PradyumnaGudluru/HealthMonotoringSystem/LPEDT-firmware/Screenshots/advertising_period.png

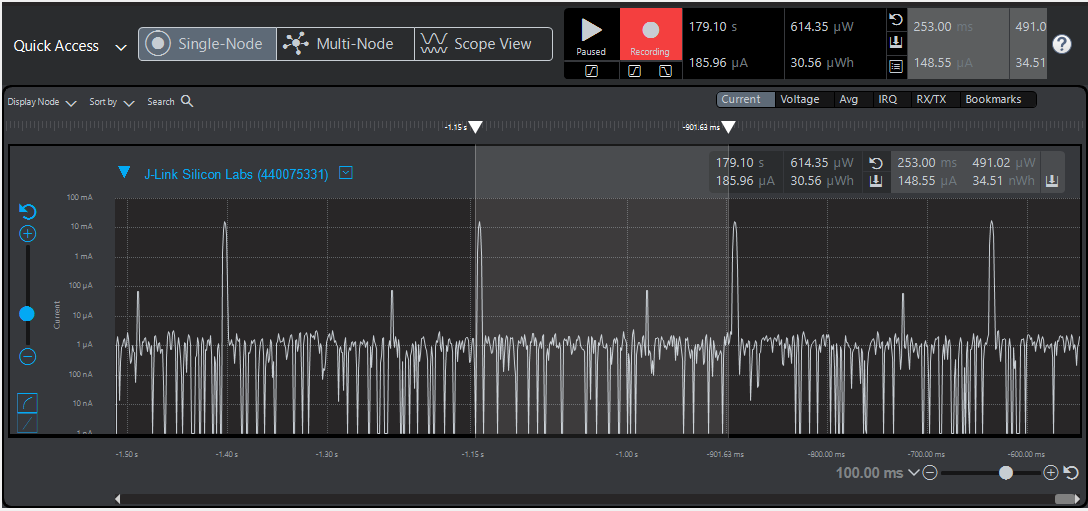
LPEDT-firmware/Screenshots/advertising_period.png
