PradyumnaGudluru/HealthMonotoringSystem/LPEDT-firmware/Screenshots/peak_current_of_advertisement.png

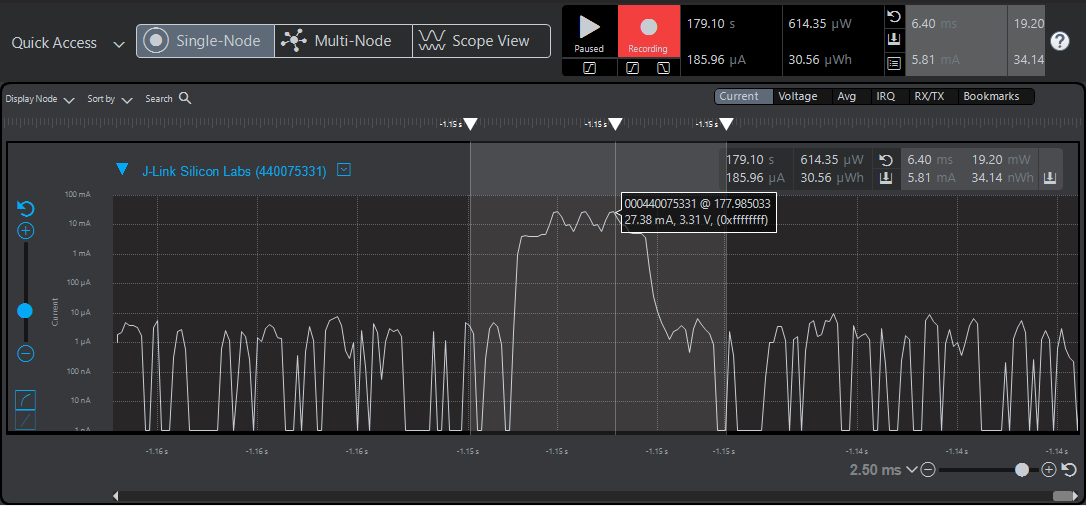
LPEDT-firmware/Screenshots/peak_current_of_advertisement.png
