PradyumnaGudluru/HealthMonotoringSystem/LPEDT-firmware/Screenshots/peak_current_phone_20ft_away.png

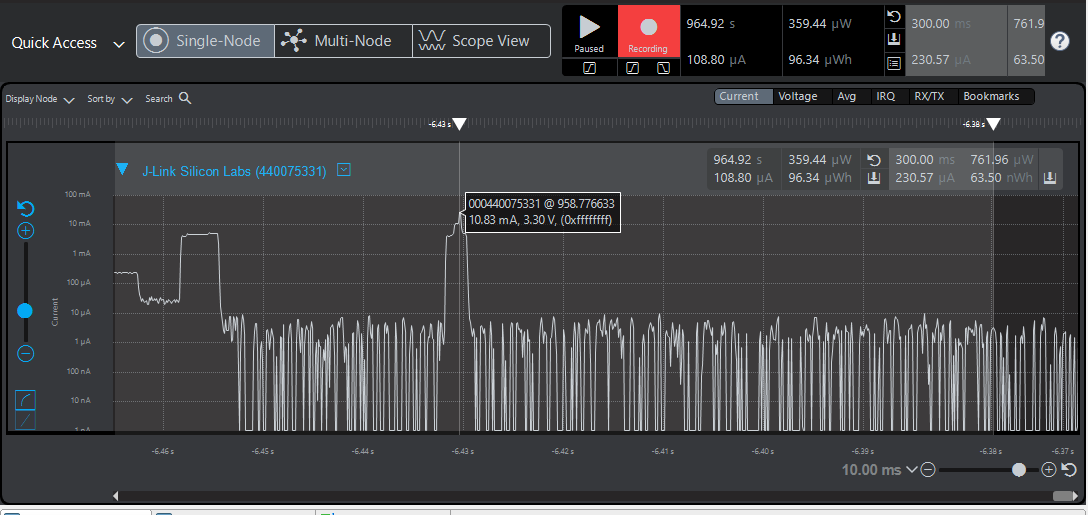
LPEDT-firmware/Screenshots/peak_current_phone_20ft_away.png
