PradyumnaGudluru/HealthMonotoringSystem/LPEDT-firmware/Screenshots/peak_current_phone_next_to.png

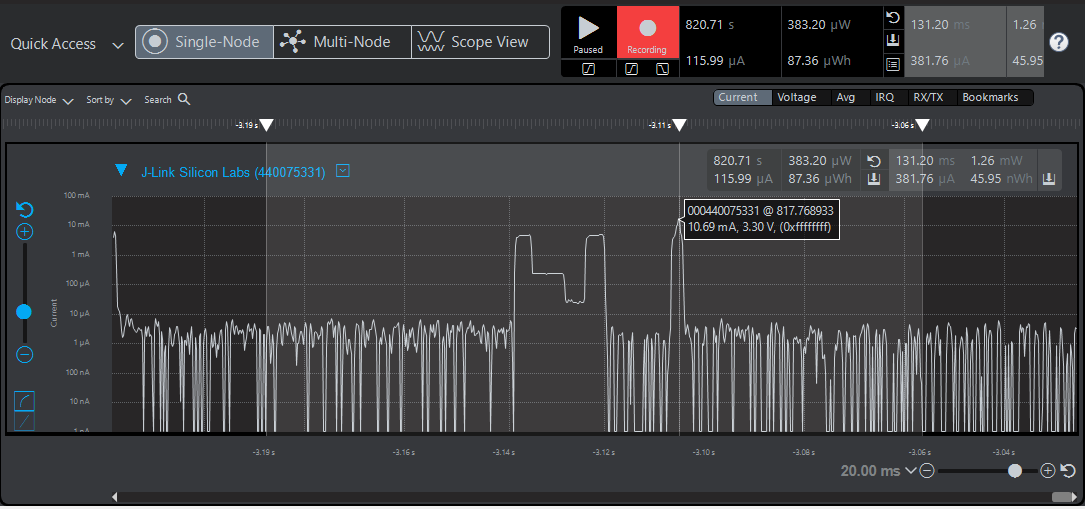
LPEDT-firmware/Screenshots/peak_current_phone_next_to.png
