PradyumnaGudluru/HealthMonotoringSystem/LPEDT-firmware/Screenshots/slave_latency.png

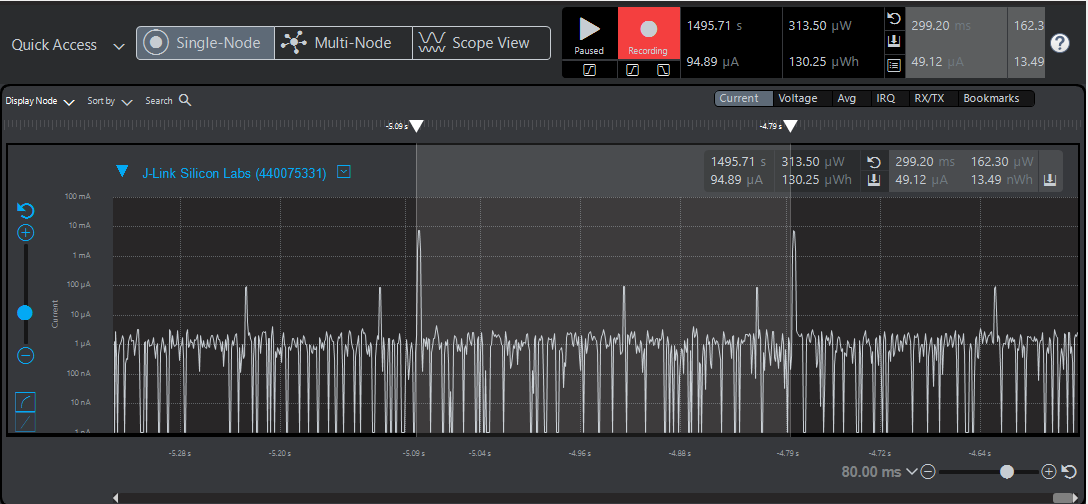
LPEDT-firmware/Screenshots/slave_latency.png
