PradyumnaGudluru/HealthMonotoringSystem/LPEDT-firmware/autogen/sl_i2cspm_init.c

/***************************************************************************//**
 * @file
 * @brief I2C simple poll-based master mode driver instance initialilization
 *******************************************************************************
 * # License
 * <b>Copyright 2020 Silicon Laboratories Inc. www.silabs.com</b>
 *******************************************************************************
 *
 * The licensor of this software is Silicon Laboratories Inc. Your use of this
 * software is governed by the terms of Silicon Labs Master Software License
 * Agreement (MSLA) available at
 * www.silabs.com/about-us/legal/master-software-license-agreement. This
 * software is distributed to you in Source Code format and is governed by the
 * sections of the MSLA applicable to Source Code.
 *
 ******************************************************************************/

#include "sl_i2cspm.h"
#include "em_cmu.h"
// Include instance config 
#include "sl_i2cspm_i2c1_config.h"
#include "sl_i2cspm_sensor_config.h"

sl_i2cspm_t *sl_i2cspm_i2c1 = SL_I2CSPM_I2C1_PERIPHERAL;
sl_i2cspm_t *sl_i2cspm_sensor = SL_I2CSPM_SENSOR_PERIPHERAL;

#if SL_I2CSPM_I2C1_SPEED_MODE == 0
#define SL_I2CSPM_I2C1_HLR i2cClockHLRStandard
#define SL_I2CSPM_I2C1_MAX_FREQ I2C_FREQ_STANDARD_MAX
#elif SL_I2CSPM_I2C1_SPEED_MODE == 1
#define SL_I2CSPM_I2C1_HLR i2cClockHLRAsymetric
#define SL_I2CSPM_I2C1_MAX_FREQ I2C_FREQ_FAST_MAX
#elif SL_I2CSPM_I2C1_SPEED_MODE == 2
#define SL_I2CSPM_I2C1_HLR i2cClockHLRFast
#define SL_I2CSPM_I2C1_MAX_FREQ I2C_FREQ_FASTPLUS_MAX
#endif

#if SL_I2CSPM_SENSOR_SPEED_MODE == 0
#define SL_I2CSPM_SENSOR_HLR i2cClockHLRStandard
#define SL_I2CSPM_SENSOR_MAX_FREQ I2C_FREQ_STANDARD_MAX
#elif SL_I2CSPM_SENSOR_SPEED_MODE == 1
#define SL_I2CSPM_SENSOR_HLR i2cClockHLRAsymetric
#define SL_I2CSPM_SENSOR_MAX_FREQ I2C_FREQ_FAST_MAX
#elif SL_I2CSPM_SENSOR_SPEED_MODE == 2
#define SL_I2CSPM_SENSOR_HLR i2cClockHLRFast
#define SL_I2CSPM_SENSOR_MAX_FREQ I2C_FREQ_FASTPLUS_MAX
#endif

I2CSPM_Init_TypeDef init_i2c1 = { 
  .port = SL_I2CSPM_I2C1_PERIPHERAL,
  .sclPort = SL_I2CSPM_I2C1_SCL_PORT,
  .sclPin = SL_I2CSPM_I2C1_SCL_PIN,
  .sdaPort = SL_I2CSPM_I2C1_SDA_PORT,
  .sdaPin = SL_I2CSPM_I2C1_SDA_PIN,
  .portLocationScl = SL_I2CSPM_I2C1_SCL_LOC,
  .portLocationSda = SL_I2CSPM_I2C1_SDA_LOC,
  .i2cRefFreq = 0,
  .i2cMaxFreq = SL_I2CSPM_I2C1_MAX_FREQ,
  .i2cClhr = SL_I2CSPM_I2C1_HLR
};

I2CSPM_Init_TypeDef init_sensor = { 
  .port = SL_I2CSPM_SENSOR_PERIPHERAL,
  .sclPort = SL_I2CSPM_SENSOR_SCL_PORT,
  .sclPin = SL_I2CSPM_SENSOR_SCL_PIN,
  .sdaPort = SL_I2CSPM_SENSOR_SDA_PORT,
  .sdaPin = SL_I2CSPM_SENSOR_SDA_PIN,
  .portLocationScl = SL_I2CSPM_SENSOR_SCL_LOC,
  .portLocationSda = SL_I2CSPM_SENSOR_SDA_LOC,
  .i2cRefFreq = 0,
  .i2cMaxFreq = SL_I2CSPM_SENSOR_MAX_FREQ,
  .i2cClhr = SL_I2CSPM_SENSOR_HLR
};

void sl_i2cspm_init_instances(void)
{
  CMU_ClockEnable(cmuClock_GPIO, true);
  I2CSPM_Init(&init_i2c1);
  I2CSPM_Init(&init_sensor);
}
