PradyumnaGudluru/HealthMonotoringSystem/LPEDT-firmware/src/driver/log.c

/*
 * log.c
 *
 */


#include <stdbool.h>

// Include logging for this file
#define INCLUDE_LOG_DEBUG 1
#include "log.h"



/**
 * @return a timestamp value for the logger, typically based on a free running timer.
 * This will be printed at the beginning of each log message.
 */
uint32_t loggerGetTimestamp()
{
    #ifdef MY_USE_SYSTICKS
    
       // Students: Look in the CMSIS library for systick routines. For debugging
       //           purposes this can provide greater resolution than a timestamp based on
       //           LETIMER0. Do not turn in any code that executes systick routines
       //           as this may effect your energy measurements and your grade.
       
       // Develop this function if you so desire for debugging purposes only
	   return getSysTicks();
	   
    #else
    
       // Students: You will eventually develop this function letimerMilliseconds()
       //           and not return 0. This will be the function to call for your graded
       //           assignments. Put this function in your irq.c/.h files.
       
       return letimerMilliseconds();
	   return (0);
	   
    #endif

} // loggerGetTimestamp



/**
 * Print a string for the Silicon Labs API error codes defined in sl_status.h
 * Depends on Components:
 *     Utilities / Status Code / Status Code Strings (sl_status.c)
 *     Utilities / Status Code / Status Code Definitions
 */
void printSLErrorString(sl_status_t status) {

  char              buffer[128+1]; // 128 chars should be long enough,
                                   // if not the string will truncated
  int32_t           result;

  // Attempt to convert the error code value into a string
  result = sl_status_get_string_n(status, (char *) &buffer[0], 128); // leave room for null terminator

  // return value:
  //   The number of characters that would have been written if the buffer_length
  //   had been sufficiently large, not counting the terminating null character.
  //   If the status code is invalid, 0 or a negative number is returned. Notice
  //   that only when this returned value is strictly positive and less than
  //   buffer_length, the status string has been completely written in the buffer.
  if ((result > 0) && (result < 128)) {
      LOG_ERROR("Error code 0x%04x is %s", (unsigned int) status, &buffer[0] );
  } else {
      LOG_ERROR("Unable to convert error code 0x%04x into a string", (unsigned int) status);
  }

} // printSLErrorString()



// This is from SSv4, left here for reference.
/**
 * Initialize logging for Blue Gecko.
 * See https://www.silabs.com/community/wireless/bluetooth/forum.topic.html/how_to_do_uart_loggi-ByI
 */

//void logInit(void)
//{
//	RETARGET_SerialInit();
//	/**
//	 * See https://siliconlabs.github.io/Gecko_SDK_Doc/efm32g/html/group__RetargetIo.html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
//	 * RETARGET_SerialCrLf() ensures each linefeed also includes carriage return.  Without it, the first character is shifted in TeraTerm
//	 */
//	RETARGET_SerialCrLf(true);
//	LOG_INFO("Initialized Logging");
//}

///**
// * Block for chars to be flushed out of the serial port.  Important to do this before entering SLEEP() or you may see garbage chars output.
// */
//void logFlush(void)
//{
//	RETARGET_SerialFlush();
//}
