PradyumnaGudluru/HealthMonotoringSystem/LPEDT-firmware/src/module/defines.h

/*
 * defines.h
 *
 *  Created on: Apr 4, 2023
 *      Author: rampr
 */

#ifndef SRC_MODULE_DEFINES_H_
#define SRC_MODULE_DEFINES_H_

#include "math.h"
#define PI (3.14)


#endif /* SRC_MODULE_DEFINES_H_ */
